AmrithaMuralidharan/ELETECT/ELETECT 2.O/ELETECT 2.O/CAD/Eletect/Eletect.SLDASM

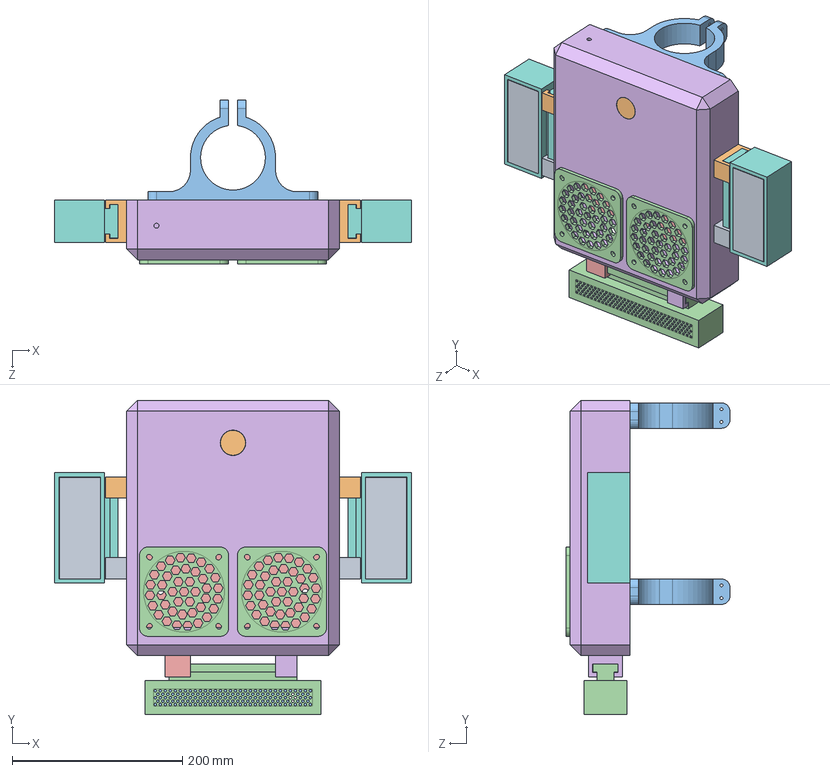
[picture p4: CAD file, 2025-10-11]
ELETECT 2.O/ELETECT 2.O/CAD/Eletect/Eletect.SLDASM
419.6 x 369.6 x 192.8 mm
Main Casing
Back Panel
speaker grill x 2
clamping x 2
LM1 x 2
LM2 x 2
Light casing x 2
light back panel x 2
UCM1
UCM2
USC
us bp
AC
AL x 2
