AmrithaMuralidharan/ELETECT/ELETECT 2.O/ELETECT RAZOR/CAD/Eletect/1.SLDPRT

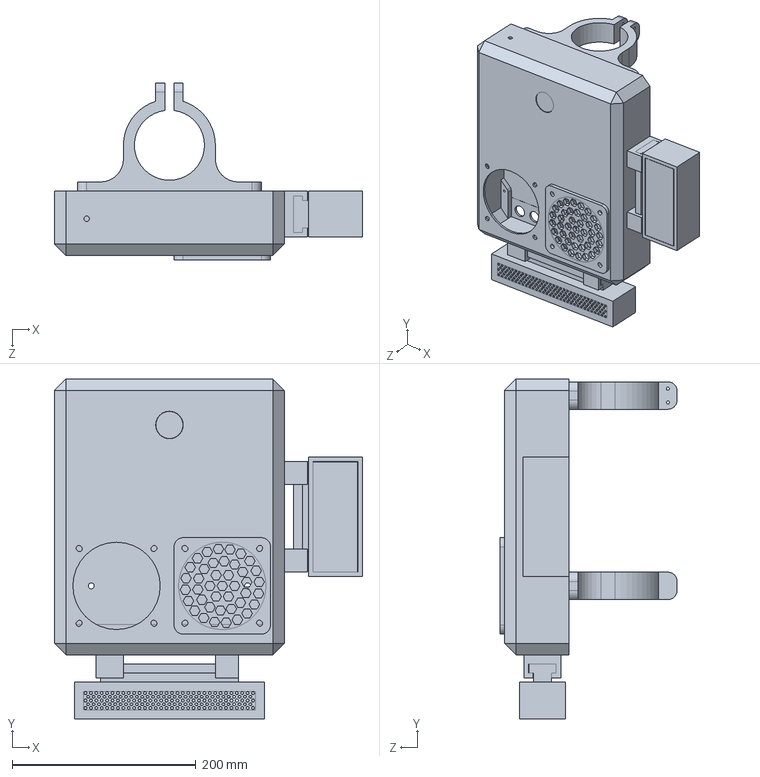
[picture p18: CAD file, 2025-10-11]
ELETECT 2.O/ELETECT RAZOR/CAD/Eletect/1.SLDPRT
335.0 x 369.8 x 192.8 mm
