AmrithaMuralidharan/ELETECT/ELETECT 2.O/ELETECT 2.O/CAD/Eletect/UCM1.SLDPRT

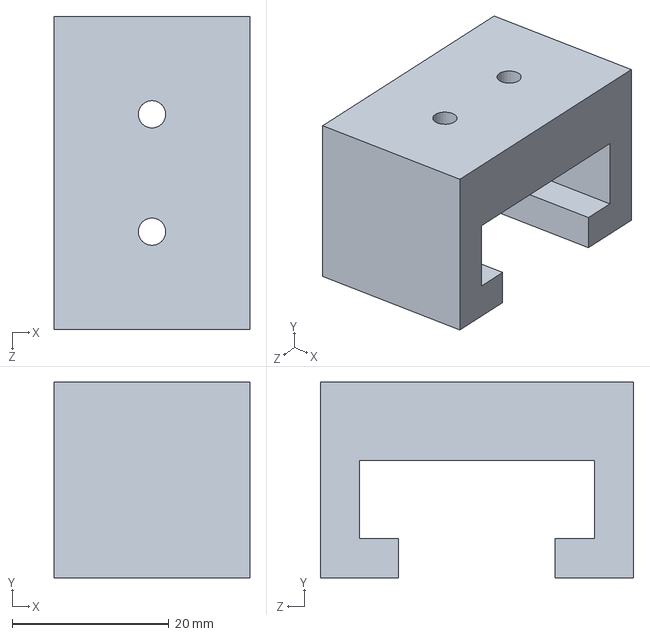
[picture p19: CAD file, 2025-10-11]
ELETECT 2.O/ELETECT 2.O/CAD/Eletect/UCM1.SLDPRT
25.0 x 25.0 x 40.0 mm
