AmrithaMuralidharan/ELETECT/ELETECT 2.O/ELETECT MINI/CAD/mini case.stl

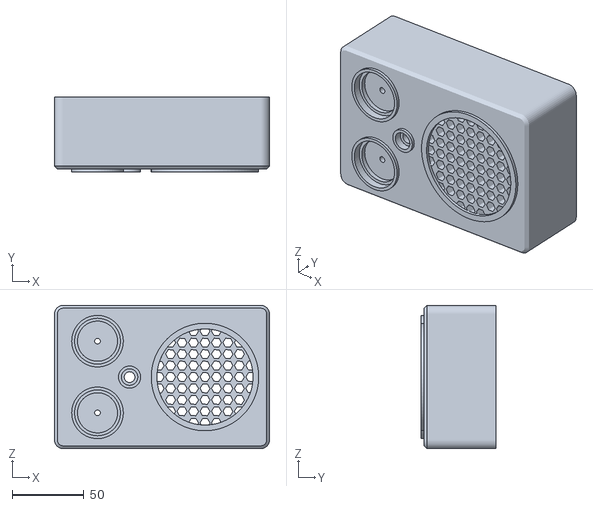
[picture p20: CAD file, 2025-10-11]
ELETECT 2.O/ELETECT MINI/CAD/mini case.stl
150.0 x 52.0 x 100.0
