AmrithaMuralidharan/ELETECT/ELETECT 2.O/ELETECT RAZOR/CAD/Eletect/clamping.SLDPRT

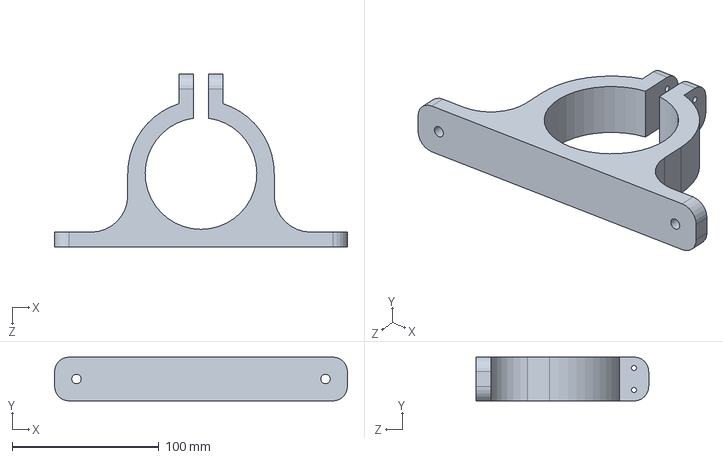
[picture p21: CAD file, 2025-10-11]
ELETECT 2.O/ELETECT RAZOR/CAD/Eletect/clamping.SLDPRT
200.0 x 30.0 x 117.8 mm
