AmrithaMuralidharan/ELETECT/ELETECT 2.O/ELETECT 2.O/CAD/Eletect/LM1.SLDPRT

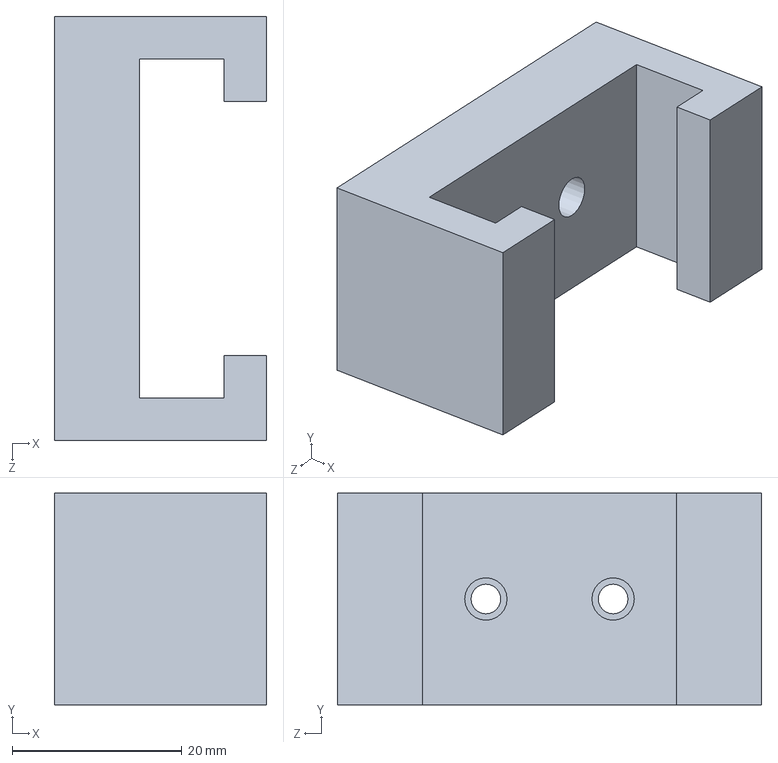
[picture p22: CAD file, 2025-10-11]
ELETECT 2.O/ELETECT 2.O/CAD/Eletect/LM1.SLDPRT
25.0 x 25.0 x 50.0 mm
