AmrithaMuralidharan/ELETECT/ELETECT 2.O/ELETECT MINI/CAD/Sketch3.dxf

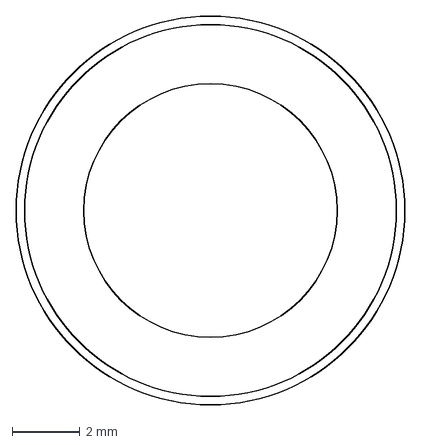
[picture p23: CAD file, 2025-10-11]
ELETECT 2.O/ELETECT MINI/CAD/Sketch3.dxf
11.5 x 11.5 mm
