AmrithaMuralidharan/ELETECT/ELETECT 2.O/ELETECT 2.O/CAD/Eletect/light back panel.SLDPRT

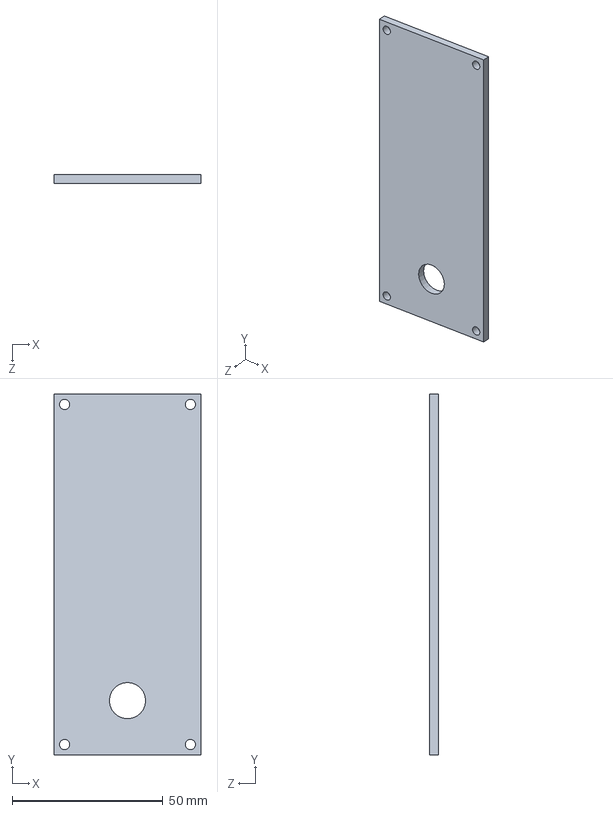
[picture p24: CAD file, 2025-10-11]
ELETECT 2.O/ELETECT 2.O/CAD/Eletect/light back panel.SLDPRT
48.6 x 119.6 x 3.00 mm
