AmrithaMuralidharan/ELETECT/ELETECT 2.O/ELETECT RAZOR/CAD/Eletect/Back Panel.SLDPRT

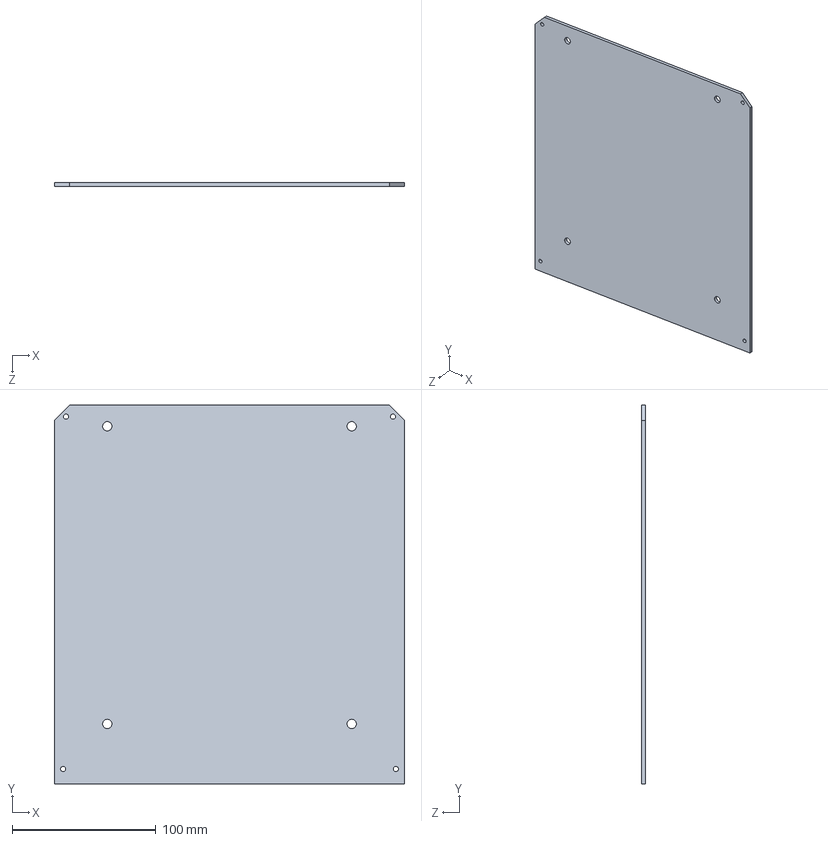
[picture p25: CAD file, 2025-10-11]
ELETECT 2.O/ELETECT RAZOR/CAD/Eletect/Back Panel.SLDPRT
243.6 x 263.6 x 3.00 mm
