AmrithaMuralidharan/ELETECT/ELETECT 2.O/ELETECT 2.O/CAD/Eletect/AC.SLDPRT

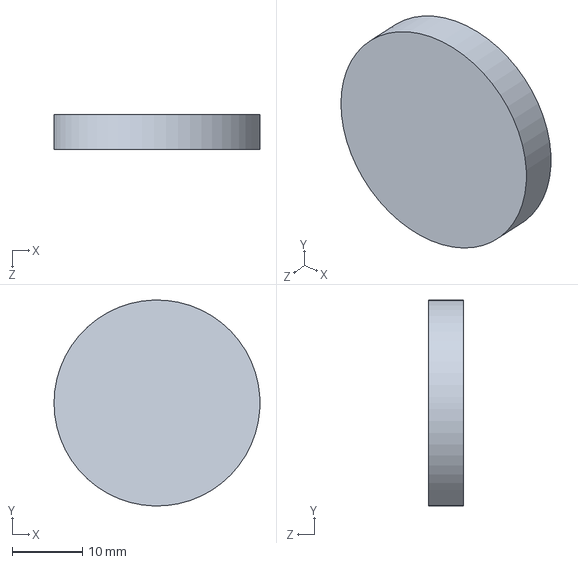
[picture p26: CAD file, 2025-10-11]
ELETECT 2.O/ELETECT 2.O/CAD/Eletect/AC.SLDPRT
29.4 x 29.4 x 5.00 mm
