AmrithaMuralidharan/ELETECT/ELETECT 2.O/ELETECT RAZOR/CAD/Eletect/LM2.SLDPRT

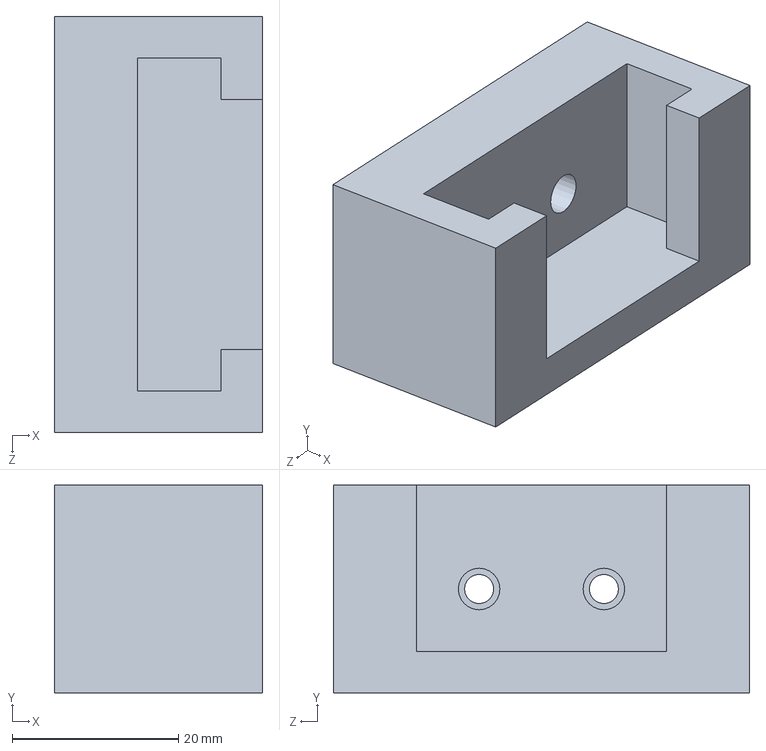
[picture p27: CAD file, 2025-10-11]
ELETECT 2.O/ELETECT RAZOR/CAD/Eletect/LM2.SLDPRT
25.0 x 25.0 x 50.0 mm
