AmrithaMuralidharan/ELETECT/ELETECT 2.O/ELETECT 2.O/CAD/Eletect/USC.SLDPRT

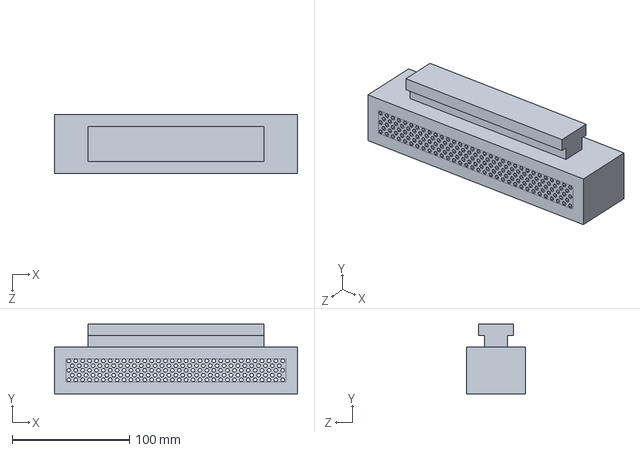
[picture p28: CAD file, 2025-10-11]
ELETECT 2.O/ELETECT 2.O/CAD/Eletect/USC.SLDPRT
207.0 x 59.6 x 50.0 mm
