AmrithaMuralidharan/ELETECT/ELETECT 2.O/ELETECT 2.O/CAD/Eletect/AL.SLDPRT

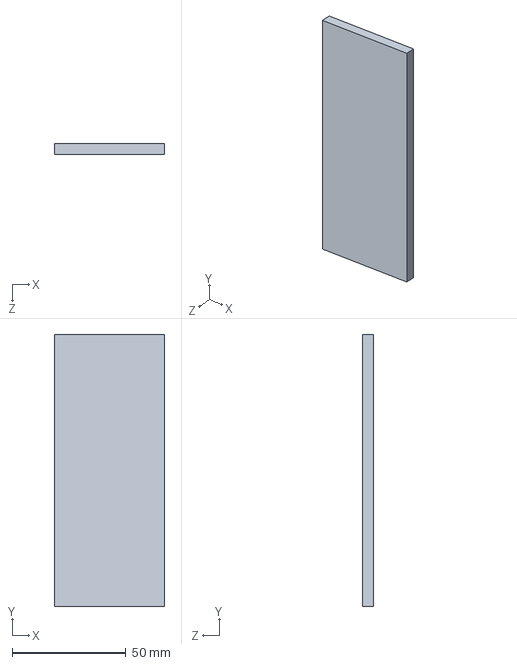
[picture p29: CAD file, 2025-10-11]
ELETECT 2.O/ELETECT 2.O/CAD/Eletect/AL.SLDPRT
48.4 x 119.4 x 5.00 mm
