AmrithaMuralidharan/ELETECT/ELETECT 2.O/ELETECT RAZOR/CAD/Eletect/Light casing.SLDPRT

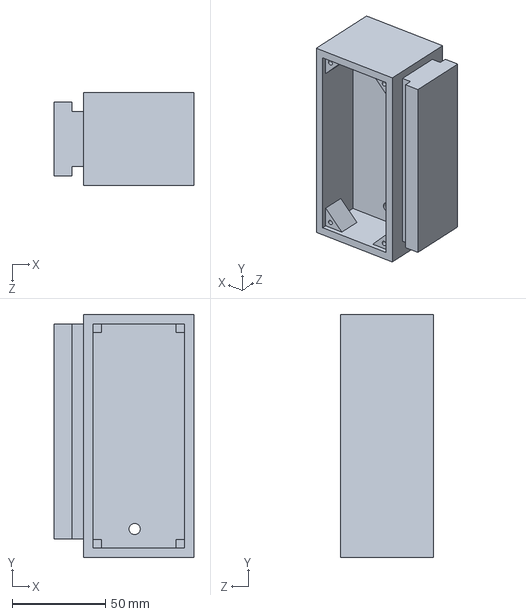
[picture p30: CAD file, 2025-10-11]
ELETECT 2.O/ELETECT RAZOR/CAD/Eletect/Light casing.SLDPRT
74.8 x 130.0 x 50.0 mm
